ChrisChrisLoLo/idawgz32/images/PXL_20240225_201037400.jpg

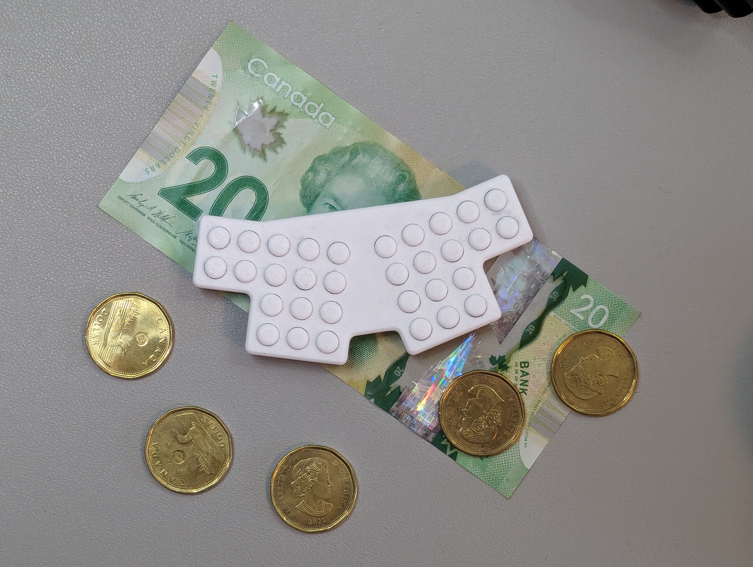
images/PXL_20240225_201037400.jpg
