ChrisChrisLoLo/idawgz32/images/PXL_20240225_223509158.jpg

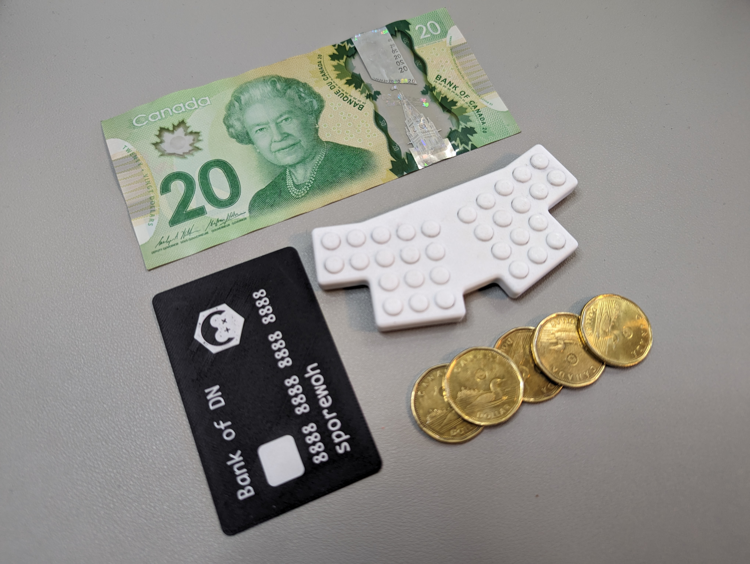
images/PXL_20240225_223509158.jpg
