ChrisChrisLoLo/idawgz32/images/PXL_20240225_225522157.jpg

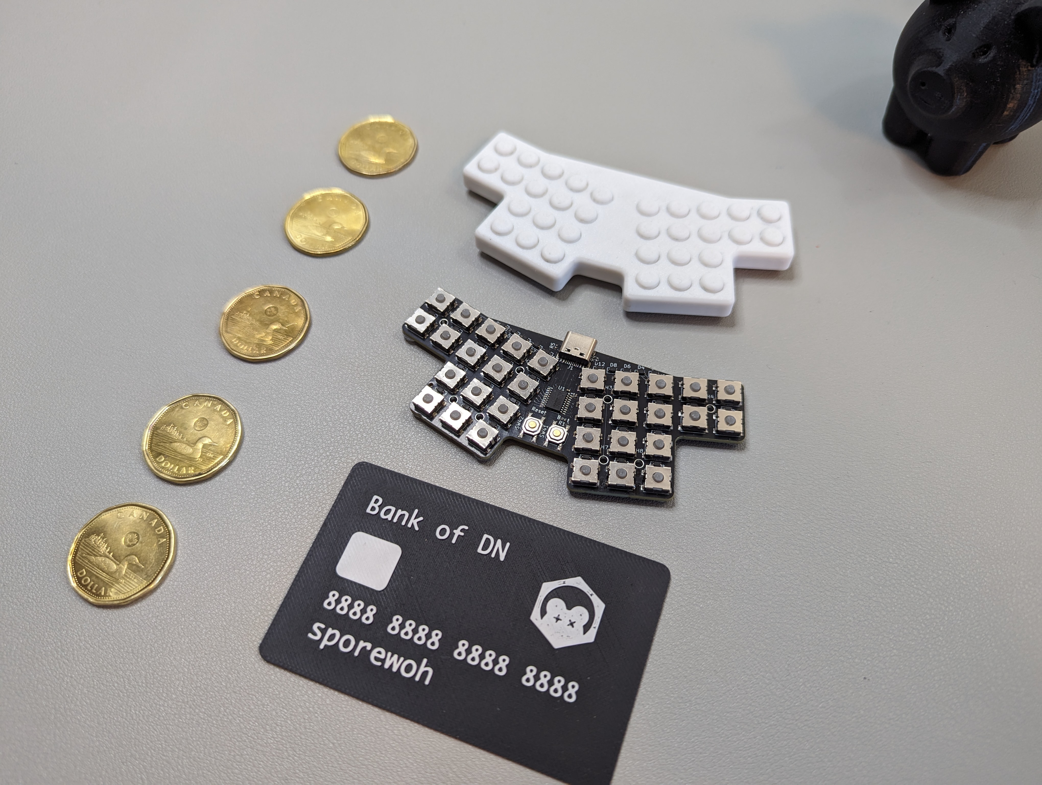
images/PXL_20240225_225522157.jpg
